LeoChizh/ups_boards/pcb2/pcb1.kicad_pcb

## KiCad design pcb2/pcb1.kicad_pcb (2026-08-14)

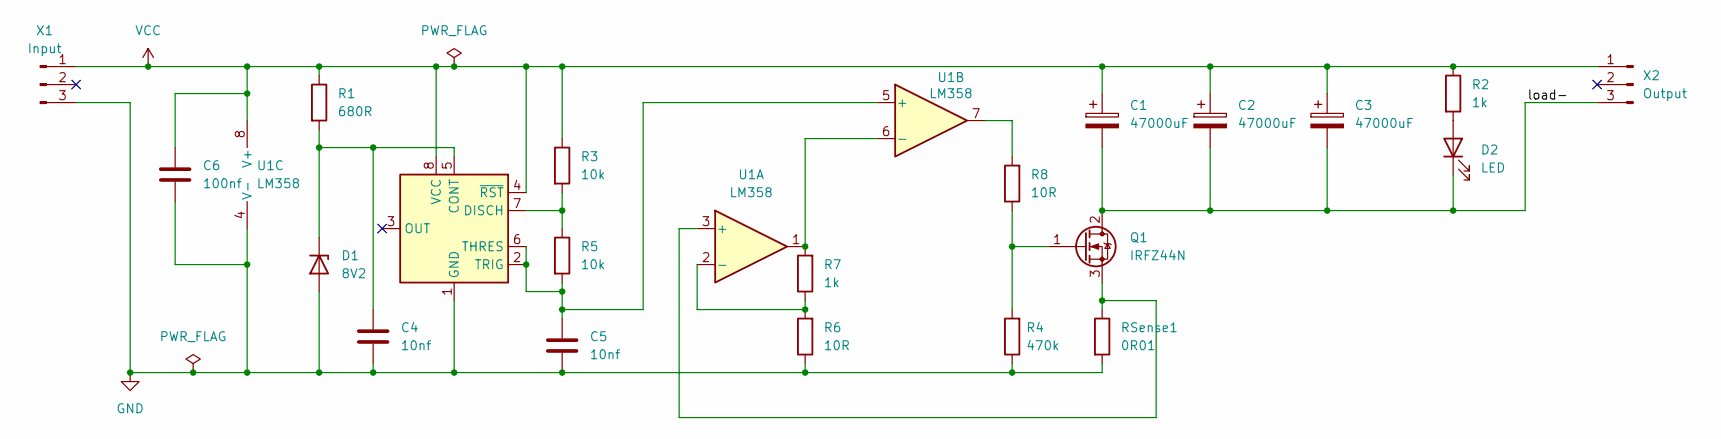
[picture p4: schematic pcb1.kicad_sch]

Parts:
C1, C2, C3: 47000uF; CP_Radial_D35.0mm_P10.00mm_SnapIn
C4: 10nf; C_Rect_L7.2mm_W3.5mm_P5.00mm_FKS2_FKP2_MKS2_MKP2
C5: 10nf; C_Rect_L7.0mm_W3.5mm_P5.00mm
C6: 100nf; C_Rect_L9.0mm_W3.3mm_P7.50mm_MKT
D1: 8V2; D_DO-35_SOD27_P7.62mm_Horizontal
D2: LED; LED_D3.0mm_Clear
Q1: IRFZ44N; TO-220-3_Vertical
R1: 680R; R_Axial_DIN0207_L6.3mm_D2.5mm_P10.16mm_Horizontal
R2, R7: 1k; R_Axial_DIN0207_L6.3mm_D2.5mm_P10.16mm_Horizontal
R3, R5: 10k; R_Axial_DIN0207_L6.3mm_D2.5mm_P10.16mm_Horizontal
R4: 470k; R_Axial_DIN0207_L6.3mm_D2.5mm_P10.16mm_Horizontal
R6, R8: 10R; R_Axial_DIN0207_L6.3mm_D2.5mm_P10.16mm_Horizontal
RSense1: 0R01; R_Shunt_d1.2mm_L10mm
U1: LM358; DIP-8_W7.62mm
U2: NE555P; DIP-8_W7.62mm
X1: Input; PhoenixContact_MSTBA_2,5_3-G-5,08_1x03_P5.08mm_Horizontal
X2: Output; PhoenixContact_MSTBA_2,5_3-G-5,08_1x03_P5.08mm_Horizontal

Connections:
/load-: C1.2, C2.2, C3.2, D2.1 (K), Q1.2 (D), X2.3
GND: C4.2, C5.2, C6.2, D1.2 (A), R4.1, R6.1, RSense1.2, U1.4 (V-), U2.1 (GND), X1.3
unnamed: C4.1, D1.1 (K), R1.2, U2.5 (CONT)
unnamed: D2.2 (A), R2.2
unnamed: Q1.1 (G), R4.2, R8.1
unnamed: Q1.3 (S), RSense1.1, U1.3 (+)
unnamed: R8.2, U1.7
unnamed: R6.2, R7.1, U1.2 (-)
unnamed: C5.1, R5.2, U1.5 (+), U2.2 (TRIG), U2.6 (THRES)
unnamed: R7.2, U1.1, U1.6 (-)
unnamed: R3.2, R5.1, U2.7 (DISCH)
VCC: C1.1, C2.1, C3.1, C6.1, R1.1, R2.1, R3.1, U1.8 (V+), U2.4 (~RST), U2.8 (VCC), X1.1, X2.1

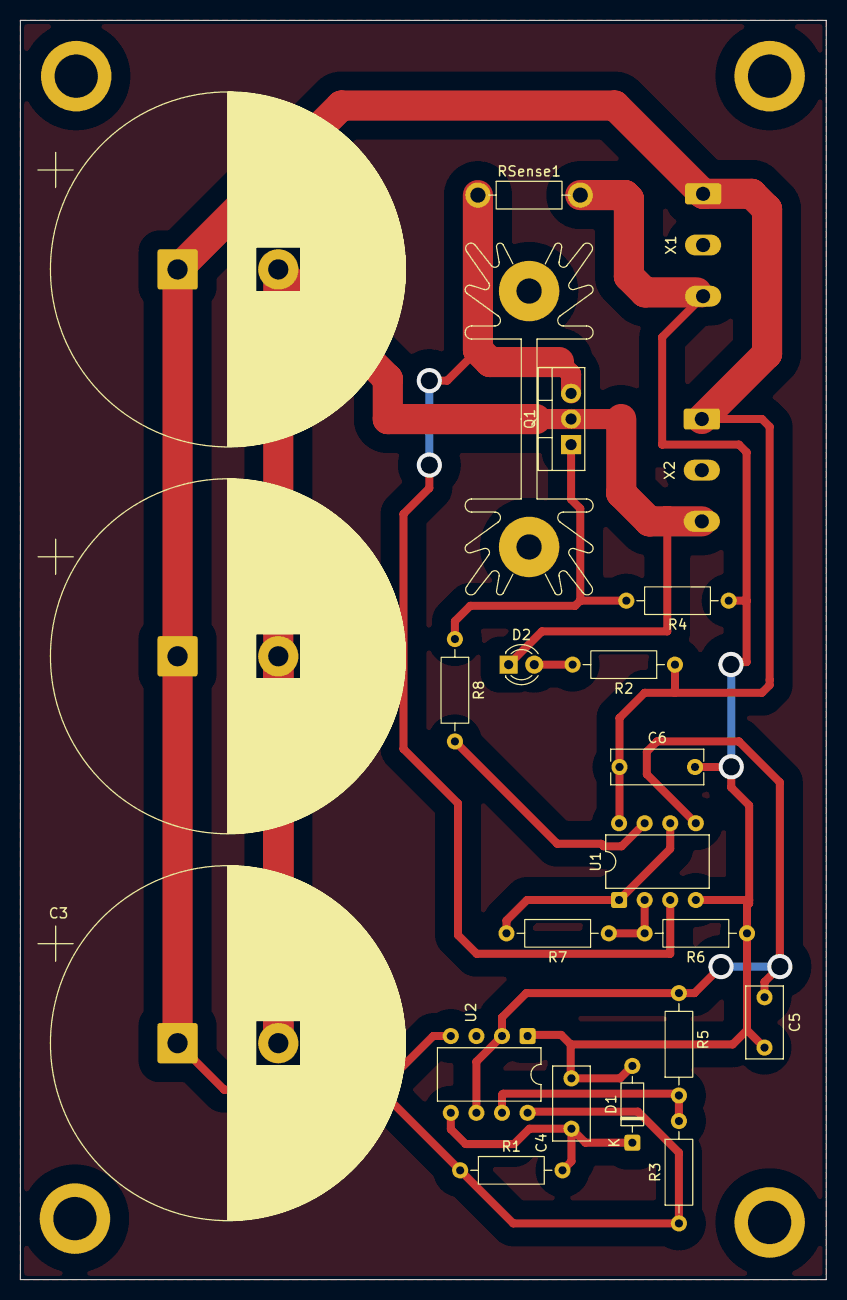
[picture p5: board pcb1.kicad_pcb from above]

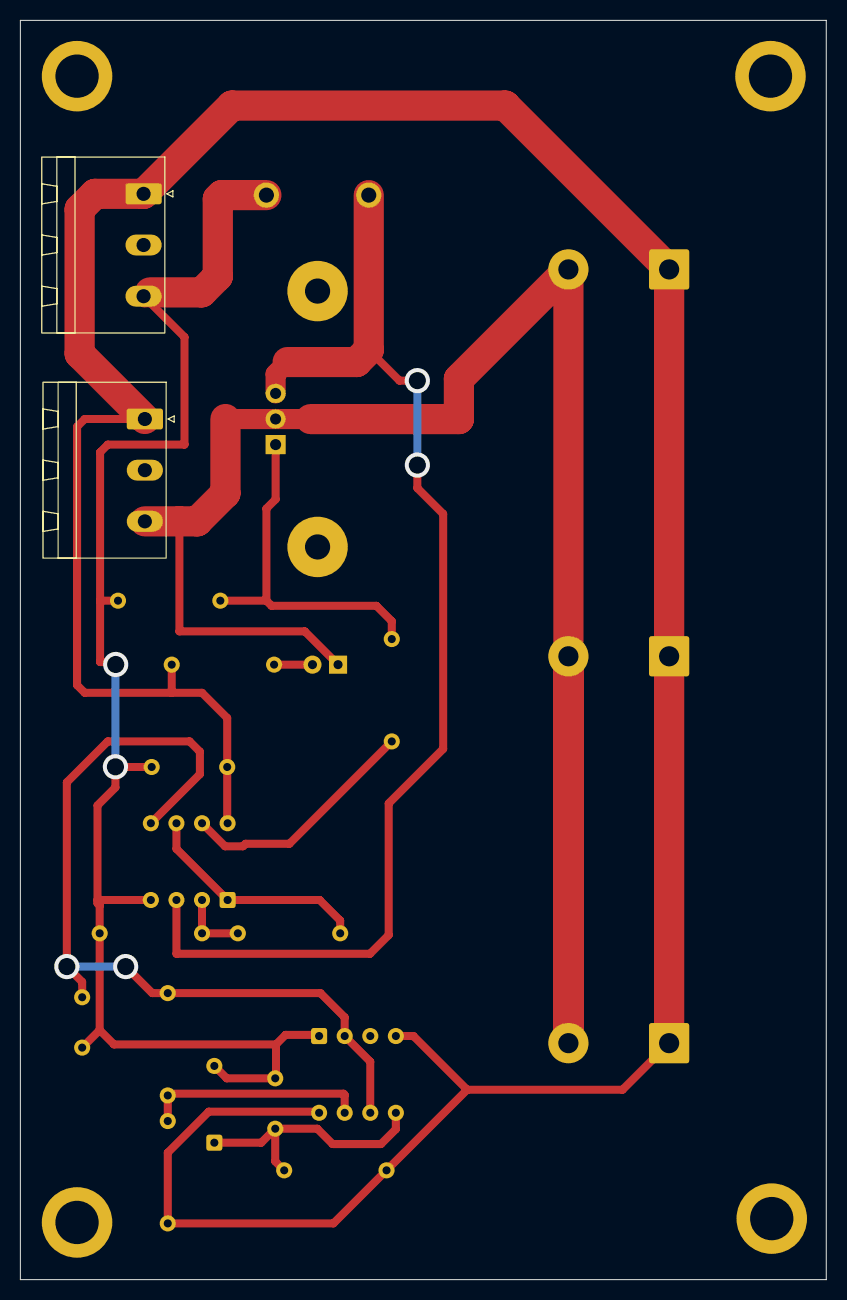
[picture p6: board pcb1.kicad_pcb from below]

Board: 2 copper layers, 80.0 x 125.0 mm, 26 parts (2 on the bottom side), 12 nets.

Other parts of the board:
mount: MountingHole_4.3mm_M4_ISO14580_Pad
mount#2, mount#3, mount#4: MountingHole_4.3mm_M4_ISO14580_Pad
